mrohner/ZVV-and-Weather-with-Wemos-D1/NexConfig.h

/**
 * @file NexConfig.h
 *
 * Options for user can be found here. 
 *
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
 THIS IS FOR THE WEMOS -- MR
 
 */
#ifndef __NEXCONFIG_H__
#define __NEXCONFIG_H__

/**
 * @addtogroup Configuration 
 * @{ 
 */

/** 
 * Define DEBUG_SERIAL_ENABLE to enable debug serial. 
 * Comment it to disable debug serial. 
 */
//#define DEBUG_SERIAL_ENABLE

/**
 * Define dbSerial for the output of debug messages. 
 */
#define dbSerial Serial1

/**
 * Define nexSerial for communicate with Nextion touch panel. 
 */

#include <SoftwareSerial.h>
extern SoftwareSerial SoftySerial;
#define nexSerial SoftySerial


#ifdef DEBUG_SERIAL_ENABLE
#define dbSerialPrint(a)    dbSerial.print(a)
#define dbSerialPrintln(a)  dbSerial.println(a)
#define dbSerialBegin(a)    dbSerial.begin(a)
#else
#define dbSerialPrint(a)    do{}while(0)
#define dbSerialPrintln(a)  do{}while(0)
#define dbSerialBegin(a)    do{}while(0)
#endif

/**
 * @}
 */

#endif /* #ifndef __NEXCONFIG_H__ */
